mackieks/MaplePad/images/IMG_20221216_191824_862.jpg

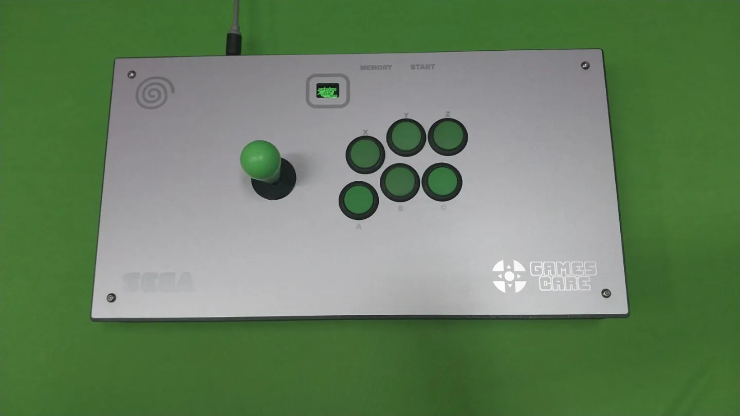
images/IMG_20221216_191824_862.jpg
