mackieks/MaplePad/images/purupuru.png

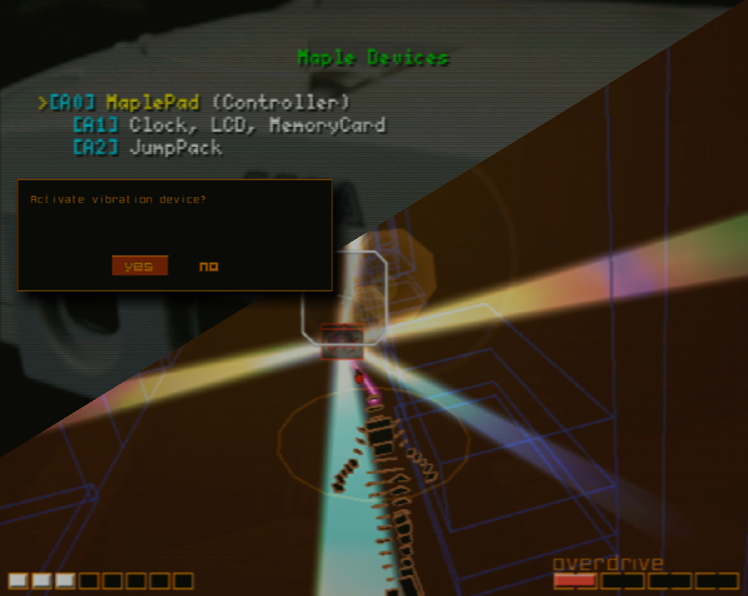
images/purupuru.png
