mackieks/MaplePad/src/ssd1331.c

/* ssd1331.c
 *  16-bit color 96x64 SPI OLED driver
 */

#include "ssd1331.h"
#include "maple.h"
#include "display.h"

#define TRUE 1
#define FALSE 0

uint8_t oledFB[96 * 64 * 2] = {0x00};

static volatile uint dma_tx;
static dma_channel_config c;

const uint8_t icon[] = {
    // MaplePad splashscreen
    0x00, 0x00, 0x00, 0x00, 0x00, 0x00, 0x00, 0x00, 0x00, 0x00, 0x00, 0x00, 0x00, 0x00, 0x00, 0x00, 0x00, 0x00, 0x00, 0x00, 0x00, 0x00, 0x00, 0x00, 0x00, 0x00, 0x00, 0x00, 0x00, 0x00, 0x00, 0x00, // 0x0010 (16)
    0x00, 0x00, 0x00, 0x00, 0x00, 0x00, 0x00, 0x00, 0x00, 0x00, 0x00, 0x00, 0x00, 0x00, 0x00, 0x00, 0x00, 0x00, 0x00, 0x00, 0x00, 0x00, 0x00, 0x00, 0x00, 0x00, 0x00, 0x00, 0x00, 0x00, 0x00, 0x00, // 0x0020 (32)
    0x00, 0x00, 0x00, 0x00, 0x00, 0x00, 0x00, 0x00, 0x00, 0x00, 0x00, 0x00, 0x00, 0x00, 0x00, 0x00, 0x00, 0x00, 0x00, 0x00, 0x00, 0x00, 0x00, 0x00, 0x00, 0x00, 0x00, 0x00, 0x00, 0x00, 0x00, 0x00, // 0x0030 (48)
    0x00, 0x00, 0x00, 0x00, 0x00, 0x00, 0x00, 0x00, 0x00, 0x00, 0x00, 0x00, 0x00, 0x00, 0x00, 0x00, 0x00, 0x00, 0x00, 0x00, 0x00, 0x00, 0x00, 0x00, 0x00, 0x00, 0x00, 0x00, 0x00, 0x00, 0x00, 0x00, // 0x0040 (64)
    0x00, 0x00, 0x00, 0x00, 0x00, 0x00, 0x00, 0x00, 0x00, 0x00, 0x00, 0x00, 0x00, 0x00, 0x00, 0x00, 0x00, 0x00, 0x00, 0x00, 0x00, 0x00, 0x00, 0x00, 0x00, 0x00, 0x00, 0x00, 0x00, 0x00, 0x00, 0x00, // 0x0050 (80)
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

static const uint8_t image_data_splash_girl_sat[12288] = {
    // ██▓▓░▓██▓▓█████████████▓▓▓▓▓▒▓▓███▓█▓██▓░█▓▓▓▒▓▓▒▒▓▓███▓▓██████▓▓▓▓▓▓▓▒██▓▓▓▓▓▓▓▓█████████████▓░
    // ███▓░▒███▒█████████████▓▓▓▓▒▓▓████▓█▓█▓▒██▓▓▒▓▓▓▒▓▓▓███▓▒▓████████▓▒▓███▓▓▓▓▓▓▓▓▓████████████▓░▒
    // ███▓░▒███▓▓███████████▓▓▓▓▓▓▓█████▓█▓▓▒███▓▓▒▓▓▓▒██▓▒████▓████████▓▓▓█████▓▓▓▓▓▓████████████▓░▒▒
    // ███▓▒▒███▓▓██████████▓▓▓▓▓▓████▓▓▒█▓▓▓████▓▒▓▓▓▓▓███▓█████▓▒▓█████▒██▓▓█████▓▓▓████████████▓░▒▒▓
    // ███▓▓░▓██▓▒██████████▓▓▓██████▓▒▒▓█▒▓█████▒▓▓█▓▒█████▓██████▓▒███▒▓████▓▓█████████████████▓▒▒▒▓▓
    // ▒███▓░▓██▓▒▒█████████████████░▒▒░█▒▓█████▒▓███▒██████▓████████▒▒▒░░░▒▒▓▓▓▒███████████████▒▒▒▓▓▓█
    // ▒███▓▒▓██▓▓▒▓██████████▓▓▓▒▓▓▓█▒█▓▒█████▓▓███▒████████▓▓▓▒▒▒░▒▒▒▒▒░░▒▒▒▒░▒░▒▓██████████▓▒▒▒▓▓▓██
    // ▒███▓▒▒██▓▓▓▓▓▓████▓▒▒▓▓▒▒▓███▒██▒██████████▓▓██████████░▒▒▒░▒▒▒▒▒░░▒▒▒░▒▒▒▒▒▒▒▒▓▓▓▓▓▒▒▒▒▒▓▓▓██▒
    // ▒▓███▒░██▓▓▓██▓▓▓▒▒▒▒▓▓▓▒▒███▓▓█▒██████████████████████▓░▒▒▒░▒▒▒▒▒░▒▒▒▒░▒▒▒▒▒▒▒▒▒▒░░▒▒▒▒▒▓▓██▓▒█
    // ▓▒███▓░▓█▓▓▓████▓▓▓▒▒█▓▒░███▓▓█▒▓██████████▓███████████▓░▒▒░▒▒▒▒▒░░▒▒▒░▒▒▒▒▒▒▒▒▒▒░░▒▒▒▒▒▓▓██▓▓██
    // ▓▒███▓░▓█▓▓▓████▓▓▓▒▓▓▓░▓███▒█▓▓██████████▓████████████▓░▒▒░▒▒▒▒▒░░▒▒▒░▒▒▒▒▒▒▒▒▒▒░▒▒▒▒▒▓███▒▓██▓
    // ▓▓▓██▓▒▒█▓▓▒████▓▓▓▒█▓▒▒███▓█▓▓██████████▓████████████▓▓∙░▒░▒░▒▒▒░▒▒▒░▒▒▒▒▒▒▒▒▒░░▒▒▒▒▒▓██▓▒███▓█
    // ▓▓▒██▓▒▒██▓▒███▓▓▓▒▒▓▓░████▒▓▒▓▓██▓▓███▓███████████▓▒░░░▒▒░∙░░▒▒▒▒▓▓▒░▒▒▒▒▒▒▒▒▒▒▒▒▒▒▓▓██▓▓██▓▓█▓
    // █▓▒▓██▒▒██▓▒███▓▓▓▒▓▓▒▓████▓▒█▓▓█▓▓███▓█████████▓▓░░▒▓▓████▓░∙▒▒▒▒██▓▒▒▒▒▒▒▒▒▒▒░▒▒▒▒▓██▒▓█▓▓█▓▓█
    // █▓▓▓██▓░▓█▓▒███▓▓▒▒█▓▒█████▒█▓▓█▓▒▓█▓▓████████▓▒░▒▓██████████▓░░▒▓██▓▒▒▒▒▒▒▒▒▒▒▒▒▒▓██▓▒█▓▓▓█▓▓█▓
    // ▓█▓▒██▓░▓█▓▒███▓▓▒▓▓▒▓████▒▓▒▒▓▓▒▓█▓▒▓███████▓▒▓██████████████▓▒∙▒▓▓▒▒▒▒▒▒▒▒▒▓▓▓▒▓██▓▒█▓▓██▓█▓██
    // ▓█▓▒██▓░▓██▒██▓▓▓▒█▓▒████▒▓▓▒▓▓▒▓▓▓░▓████████▓██████████████████▓∙▒▒▒▒▒▒▒▒▒▒▓██▓▓▓█▓▓▓▒▓█▓▓█▓███
    // █▓▓▓▓█▓▒▒██▓▓█▓▓▒▒█▒▓███▓▓▓▒▓▓▒▓▓▒▒▒█████████████████████████████▓∙▒▒▒▒▒▒▒▒▒▓████▓▓▒▓▒██▓▓▓▓████
    // █▓▓▓▒██▒░██▓▓█▓▓▒▒▓▒███▓▓█▒▓▓▒▒▓▒▒▓▓██████████████████████████████▓∙▒▒▒▒▒▒░▒▓█▓█▓▓▓▒▓██▒▓▓▓█████
    // ██▓▓▒██▓░██▓▓█▓▓▒▓▓▒██▓▓█▓▒▓▒▒▓▒▒▓▓████████████████████████████████▓░▒▒▒▒▒░▒▓▒▓▓▓▓▒▓▓▓▒▓▓▓██████
    // ██▓▓▒▓█▓∙▓██▓█▓▓▒█▓▒█▓▓▓█▒▓▒▒▒░▒▓▒▓█████████████████████████████████▒░▒▒▒▒░▒▒▒▓▓▓▒▓▓▓▒▓▒████████
    // ███▓▓▓█▓░▓██▓█▓▒▓█▓▓█▓▓█▓▓▓▒▒░▒▓▓▓███████████████████████████████████▒░▒▒▒▒▒▒▒▒▒▒▓▓▒▒▓▒█████▓███
    // ███▓▓▓██▒▓██▓█▓▓▓█▓██▓▓█▓█▓▓▒▒▒▓▓▓███████████████████████████████████▓░▒▒░▒▒▒▒▒▒▒▓▒▒▓▒▓███▓▓████
    // ████▓▓▓█▓▒██▓█▓▓▓█▒██▓█████▒▓▒▓▓▓█████████████████████████████████████▒▒░▒▒▒▒▒▒▒▒▒▒▒▒▓██▓▒▓█████
    // ████▓▓▓██▒██▓██▓██▓██▓█▓██▓▓▒▓▓▒██████████████████████████████████████▓░░▒▒▒▒▒▒▒▒▒▒▒▓▓█▓░▓████▓▓
    // █████▓▓██▒███▓█▓██▓████▓██▓▓▒▓▓▓██████████████████████████████████████▓░▒▒▒▒▒░▒▒▒▒▒▓▓▓▒▒▓███▓▓▓▓
    // █████▓▓██▓▓██▓▓▓██▓███▓▓▓▓▓▓▒▓▒████████████████████████████████▓██████▓▒░▒▒▒▒▒▒▒▒▒▓▓▓▒▒▓███▓▓▓▒▒
    // ███████▓█▓▓███▓▓██▓███▓▓▒▓▒▒▒▓▓▓▓███████████████████████████████▓▓████▓▒▒▒▒▒▒▒▒▒▒▒▓▓░▒▓▓█▓▓▓▒░▒▒
    // ▓██████▓██▓███▓▓██▓███▒▒▒▓▒▒▒▒▒▓▓▒▒██████████████████████████▓▓▓█████▓▓▒░░▒▒▒▒▒▒▒▒▓░▒▓▓█▓▓▓▒▓▓▓▓
    // ▓██████▓██▓███▓▓█████▓▒▒▒▒▒░▒▒▓███▒████████████████████████████████▓▓▓▓▒░▒▒▒▒▒░▒▒▒▒▒▓▓▓▓▓▓▓▓▓▓▓█
    // ▒▓████████▓████▓█████▓▒░▒▒░░▒▒████████████████████████████████████▒▓▒░▓░▒▒▒▒▒▒▒▒▒▒░▒▓▓▒▓▓▓▓▓▓▓▓▓
    // ▒▒▓████████████▓█████▓▒░▒▒▒▒▒▓██▓█████████████████████████████████▒▒▒▒▓░░░▒▒▒▒▒▒▒░▒▓▓▒▒▒░▓▓▓████
    // ▓▒▒▓█████████████████▓▒▒▒▒▒░▒▓▓█▒▒█████████████████████████████████▒▒▒▓▒▒░▒▒▒▒▒▒░▒▒▒▒▒▒░░▒▓▓████
    // ▓▒▒▒█████████████▓███▓░▒▒▒░░█▓▓▒▒▓█████████████████████████████████▓▒∙▒▒░▒▒▒▒▒▒░▒▒▒▒▒▒░░░▓▓▓████
    // ▓▓▒▒▓████████████████▒▒▒▒▒▒██▓▒▒█████▓█████████████████████████████▒▒∙▒░░▒▒░▒▒▒▒▒▒▒▒▒░░░▒▓▓▓████
    // ▓▓▓▓▓████████████▓▓██▒▒▒▒▒▓██▓▒▓███████▓██████████████████████████▒█▒▒░∙▒▒▒▒▒▒░▒▒▒░▒░░░▒▓▓▓█████
    // ▒▒▒▓▒▓████████████▓█▓▒▒▒▒▒███▓▒▓██▓███▓▓█████▓███████████████████▓▓█▒▒∙∙▓▒▒▒▒░▒▒▒░▒▒░░▒▓▓▓▓▓████
    // ▓▒▒▓▓▓████████████▓█▓▓▒▒▒▒█▓██▓▒▓█▓███▓████████████████████████▓█▓▓▓▓∙∙▒█▒▒▒▒▒▒▒▒▒▒░░▒▓▒▒▒▒▓▓▓█▓
    // ▓▓▒▒▓▓▓████████████▓▓▒▒▒▒▒▓▓██▓▒▓▓▓███▓█████████████████▓█████████▒∙∙∙▒▓█▓▒▒▒▒▒▒▒▒░░▒▓▒▒▒▒▒▒▓▓▓▓
    // ░▒▒▓▓▓▓▓███████████▓▓▒▒░▒▒▒▓▓█▓░█▒▓▓▓████████████▓▓▒▒▓▒▒██████████▓▓░░▓██▓▒▒▒▒░▒▒▒▒▒▒▒░░░▒▒▒▓▒▒▓
    // ▒▒▓▓▓▓▓▓███████████▓▒▒▒▒▒▒▒▒▒▒░▓▒░▓▓█▓█████████▓▓█▒██▓▓▓▓██████████▓████▓▒▒▓▒▒▒░▒▒▒▒▒▒▒▓▒▒▒▓▓▓▓▓
    // ▓▒▓▓▓▓▓██████████▓█▓▒▒▒▒▒▒▒▒▒▓█▒▒░▒▓██████████████▒██∙▓▓▒██████████▓███▓▒▓▓▓▒▒▒▒▒▒▒▒▒▒▒▒░▒▒▓▓▓▓▓
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
